nabeellagi/LongCat/enclosure/rawrenders/board.png

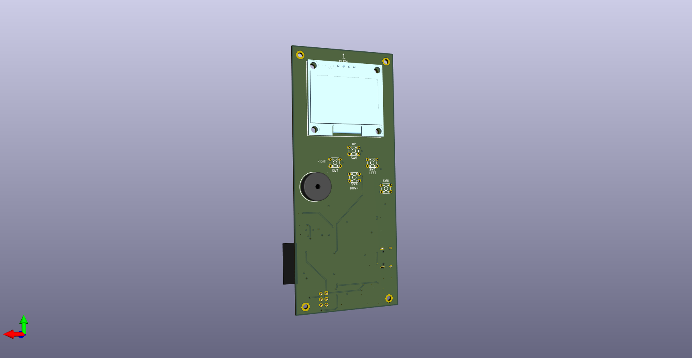
enclosure/rawrenders/board.png
