nabeellagi/LongCat/enclosure/rawrenders/console1withsticker.png

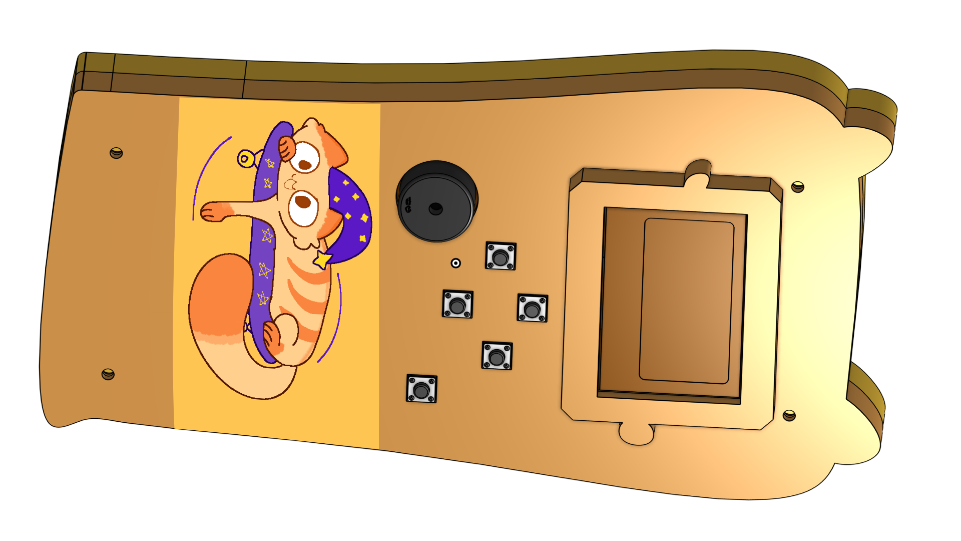
enclosure/rawrenders/console1withsticker.png
