nabeellagi/LongCat/enclosure/rawrenders/console2.png

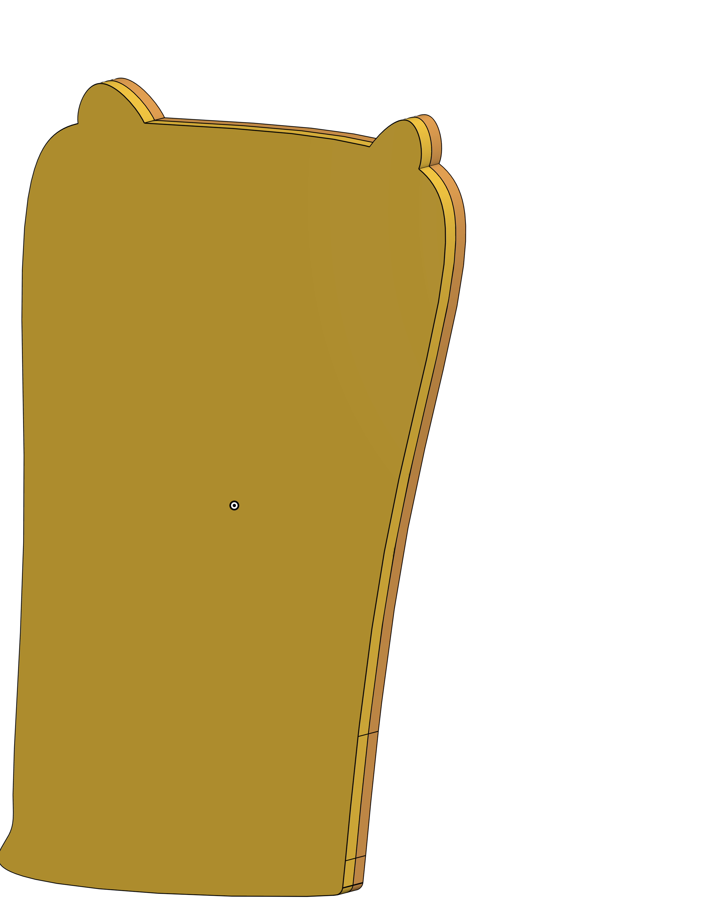
enclosure/rawrenders/console2.png
