nabeellagi/LongCat/enclosure/rawrenders/console2withsticker.png

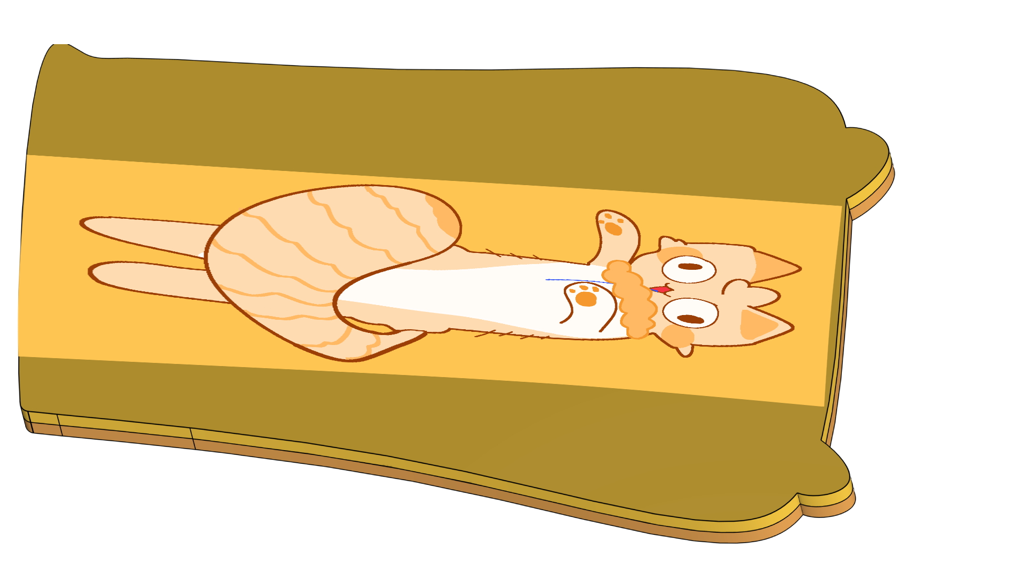
enclosure/rawrenders/console2withsticker.png
