nabeellagi/LongCat/enclosure/rawrenders/console12.png

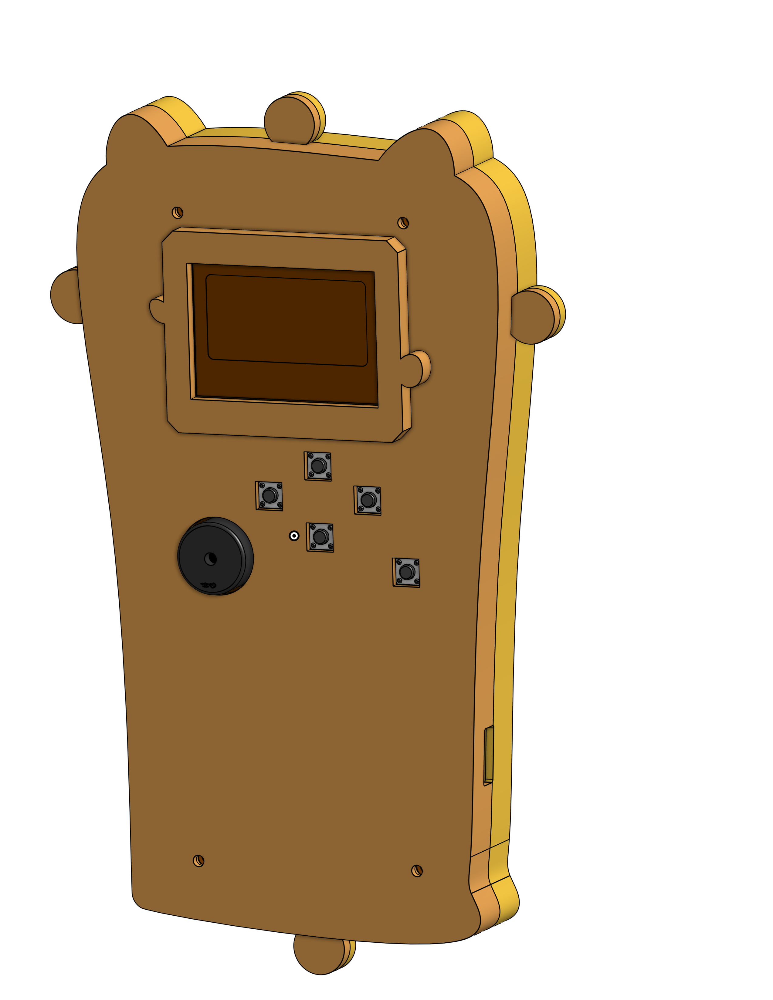
enclosure/rawrenders/console12.png
