nabeellagi/LongCat/enclosure/rawrenders/pb1.png

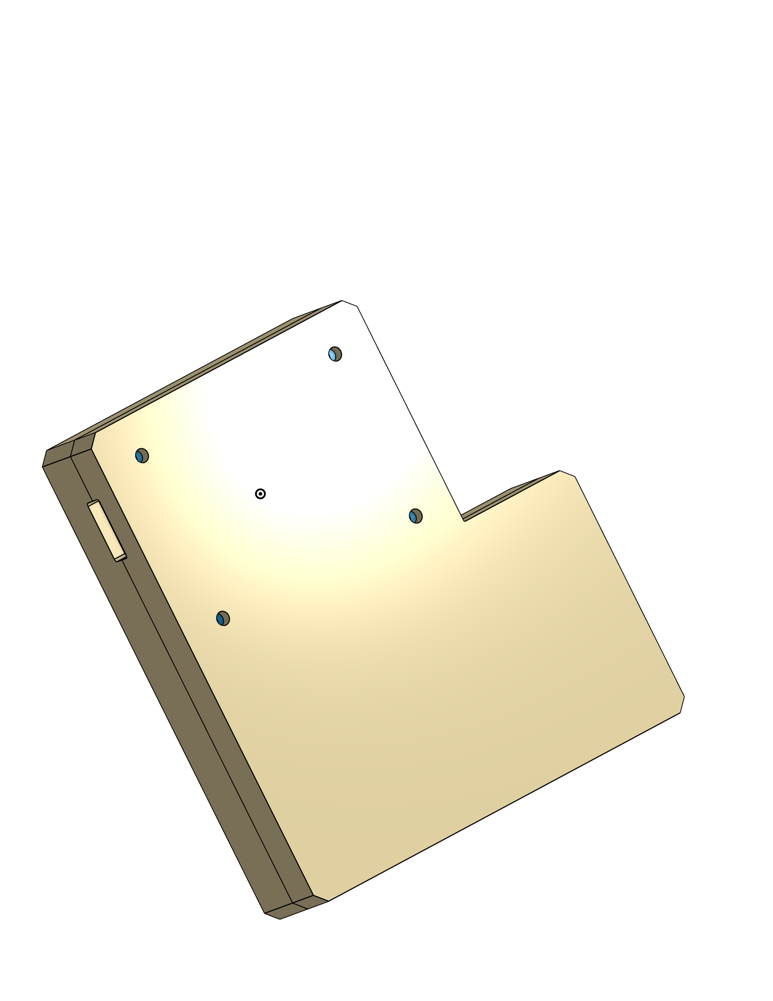
enclosure/rawrenders/pb1.png
