nabeellagi/LongCat/stickers/longcat.png

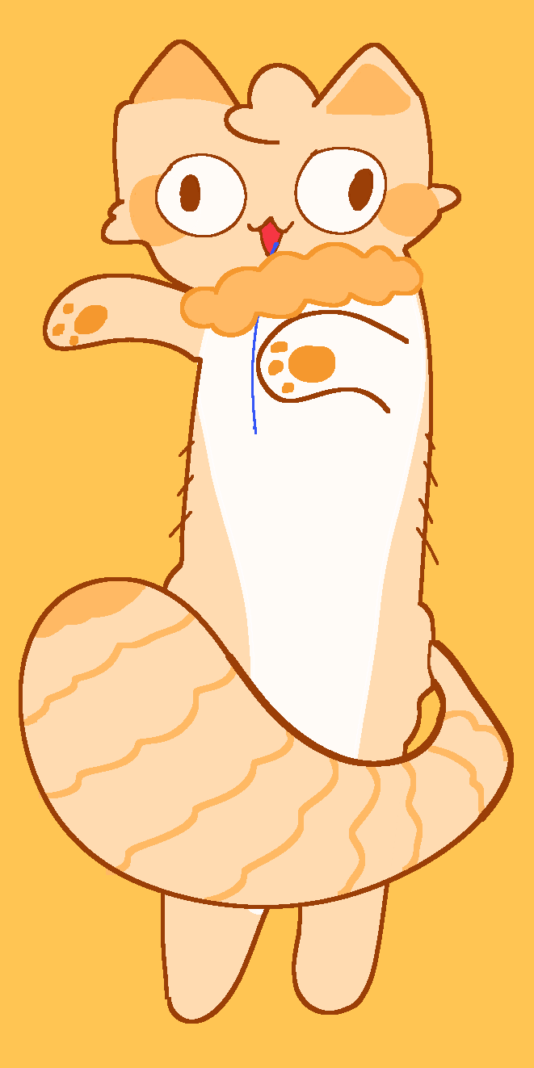
stickers/longcat.png
