nabeellagi/LongCat/stickers/tiredfox.png

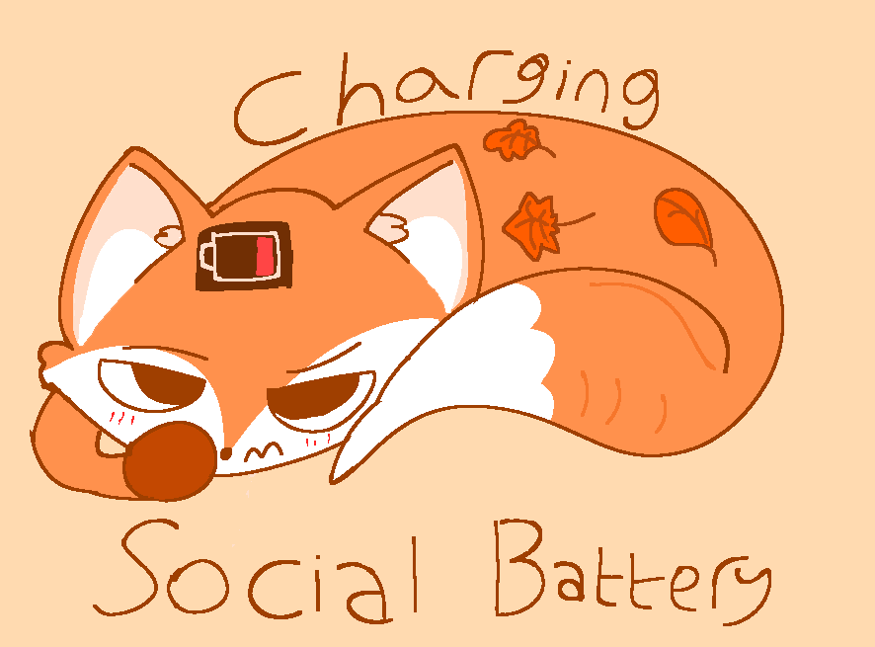
stickers/tiredfox.png
